raffsalvetti/FingerGrinder/pictures/2020-06-28 16.21.05_mod.jpg

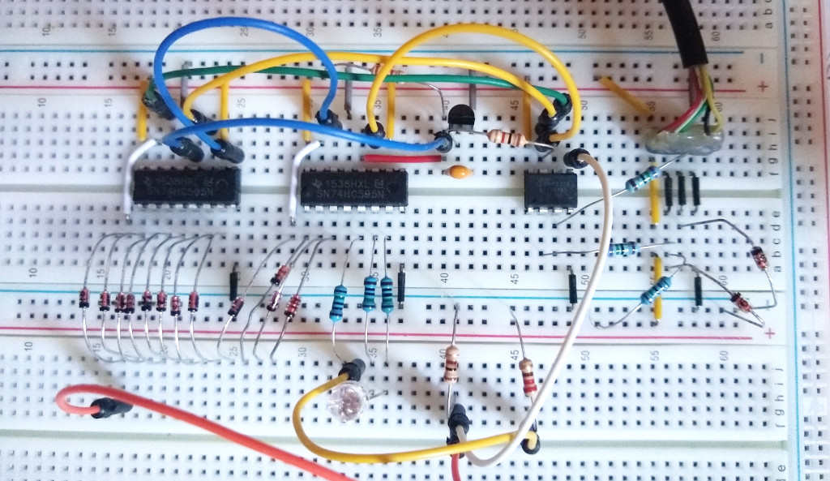
pictures/2020-06-28 16.21.05_mod.jpg
