raffsalvetti/FingerGrinder/pictures/2020-06-28 16.21.20.jpg

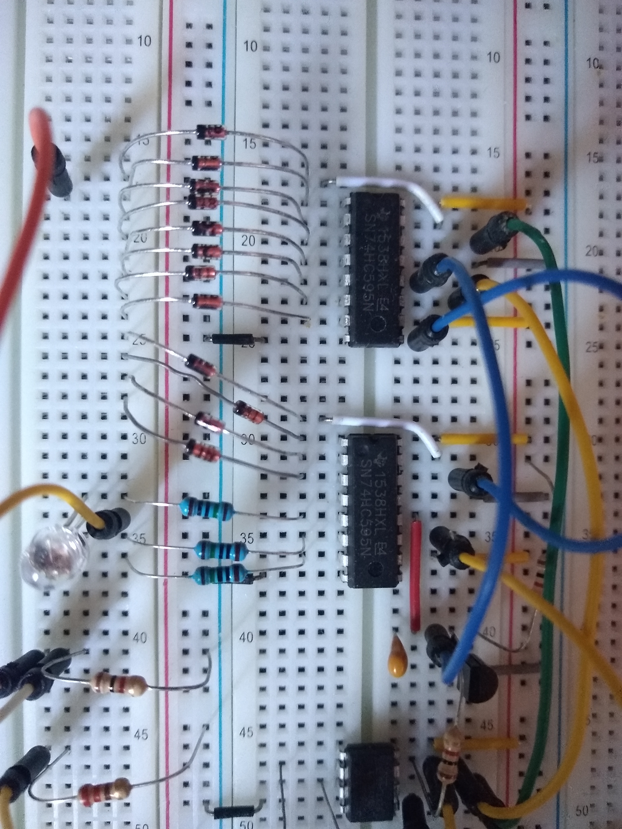
pictures/2020-06-28 16.21.20.jpg
