raffsalvetti/FingerGrinder/pictures/2020-07-19 19.21.56.jpg

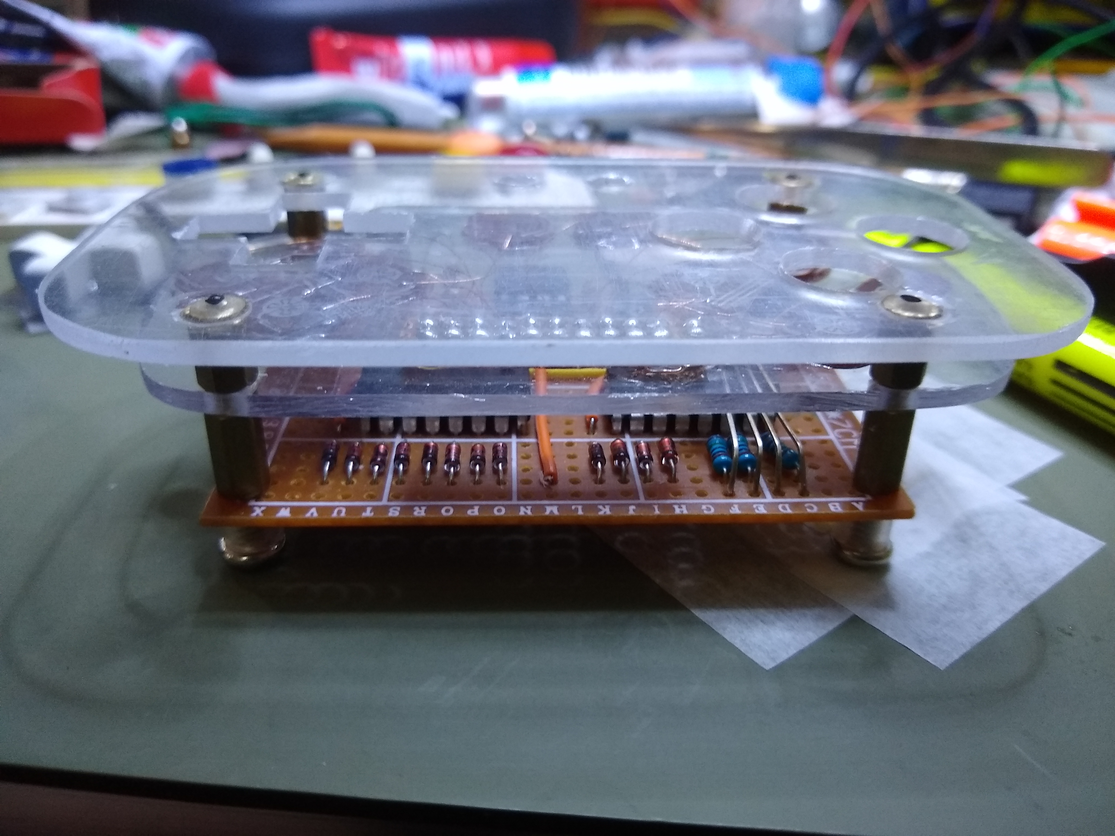
pictures/2020-07-19 19.21.56.jpg
