raffsalvetti/FingerGrinder/pictures/2020-07-19 19.22.34.jpg

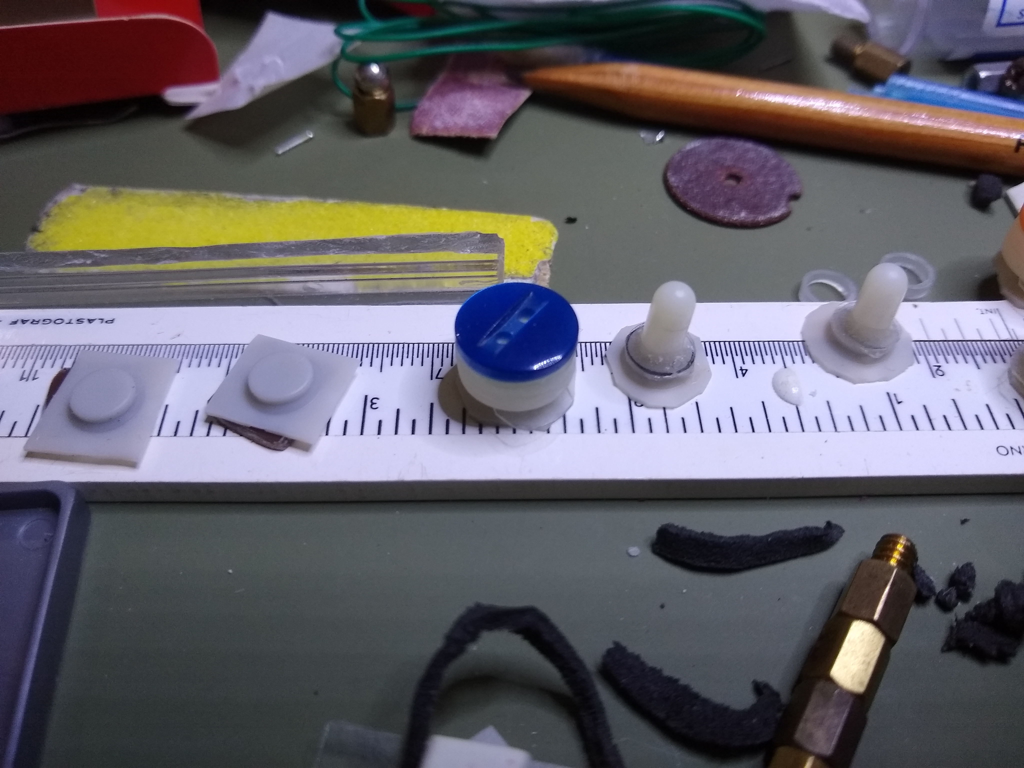
pictures/2020-07-19 19.22.34.jpg
