raffsalvetti/FingerGrinder/pictures/2020-07-19 19.22.51_mod.jpg

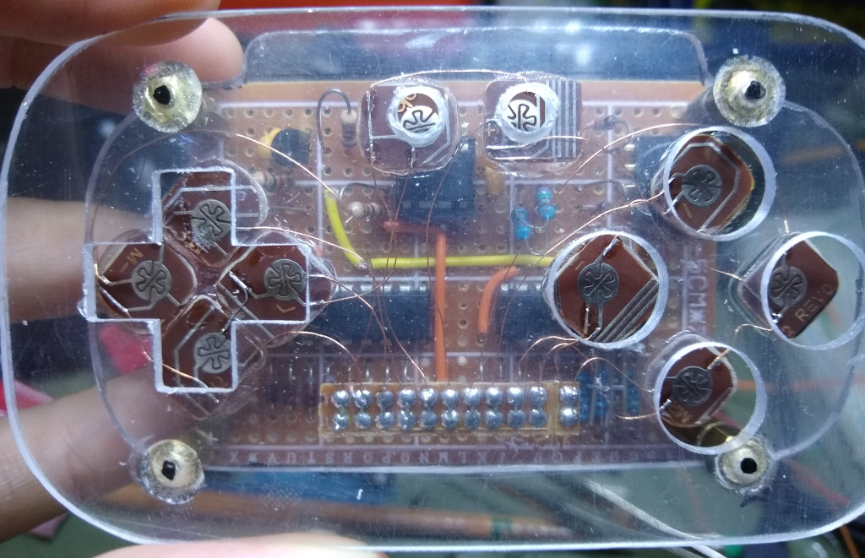
pictures/2020-07-19 19.22.51_mod.jpg
