raffsalvetti/FingerGrinder/pictures/2020-07-19 19.23.18.jpg

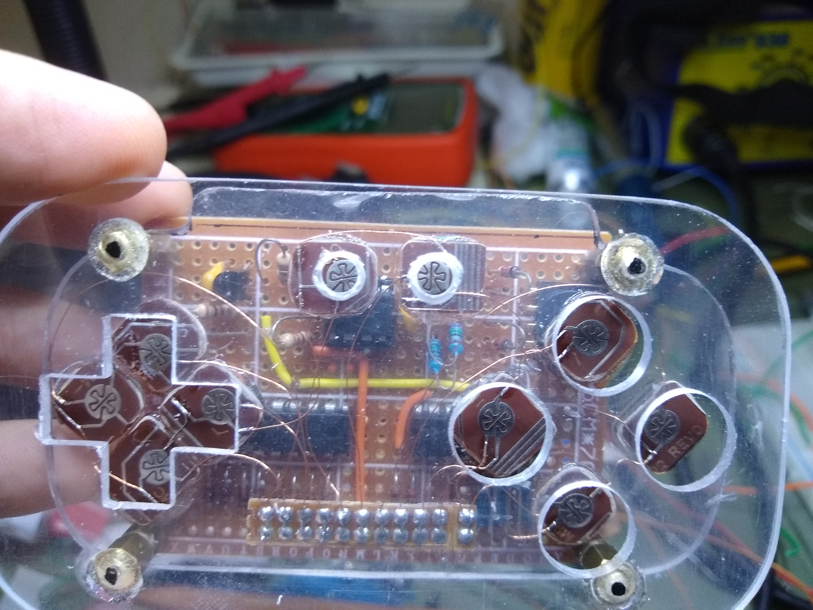
pictures/2020-07-19 19.23.18.jpg
