raffsalvetti/FingerGrinder/pictures/2020-07-19 19.24.29.jpg

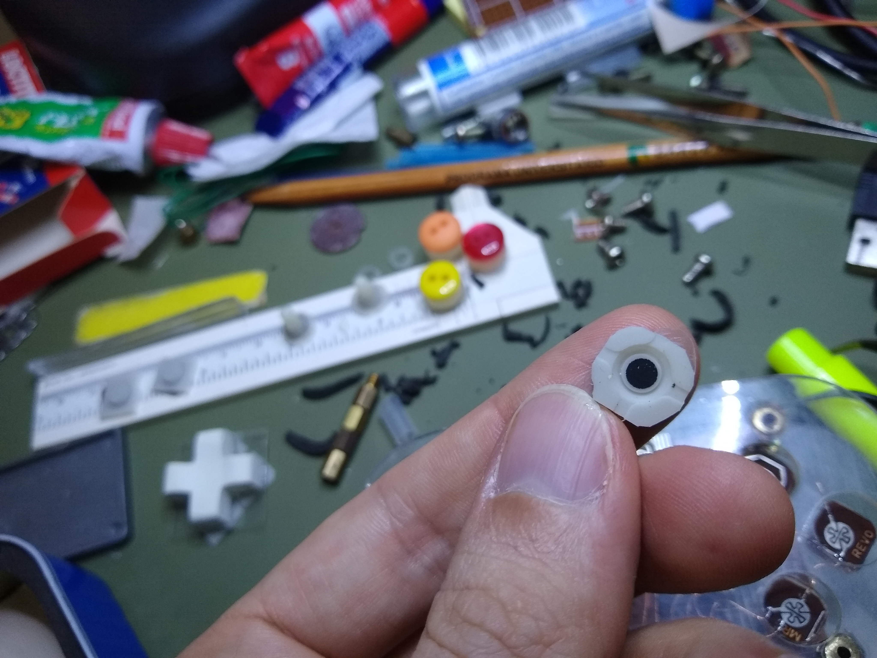
pictures/2020-07-19 19.24.29.jpg
