raffsalvetti/FingerGrinder/pictures/2020-07-21 17.19.35.jpg

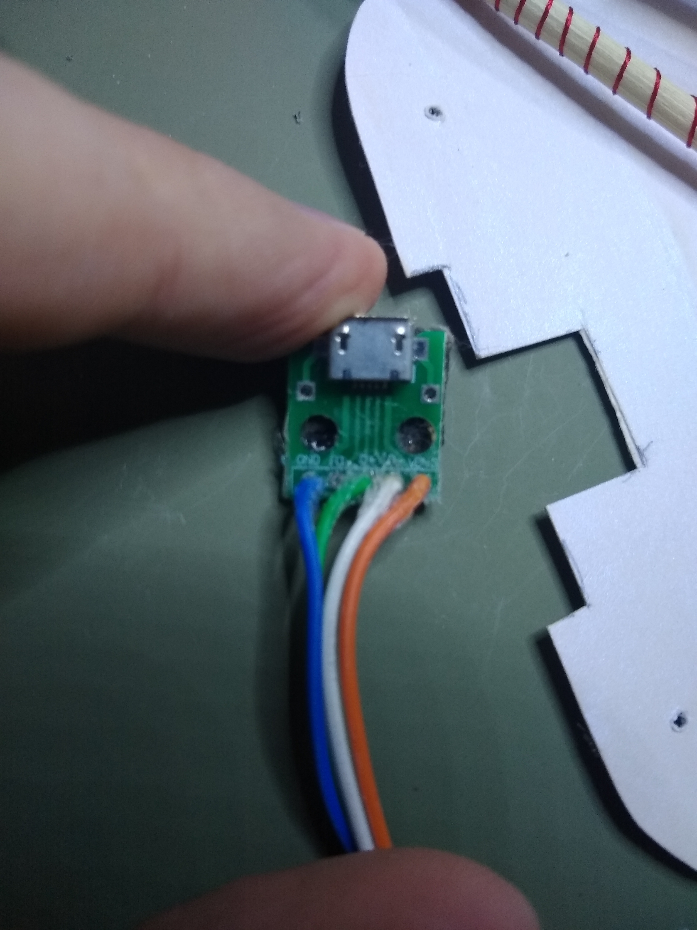
pictures/2020-07-21 17.19.35.jpg
