raffsalvetti/FingerGrinder/pictures/2020-07-24 15.05.28.jpg

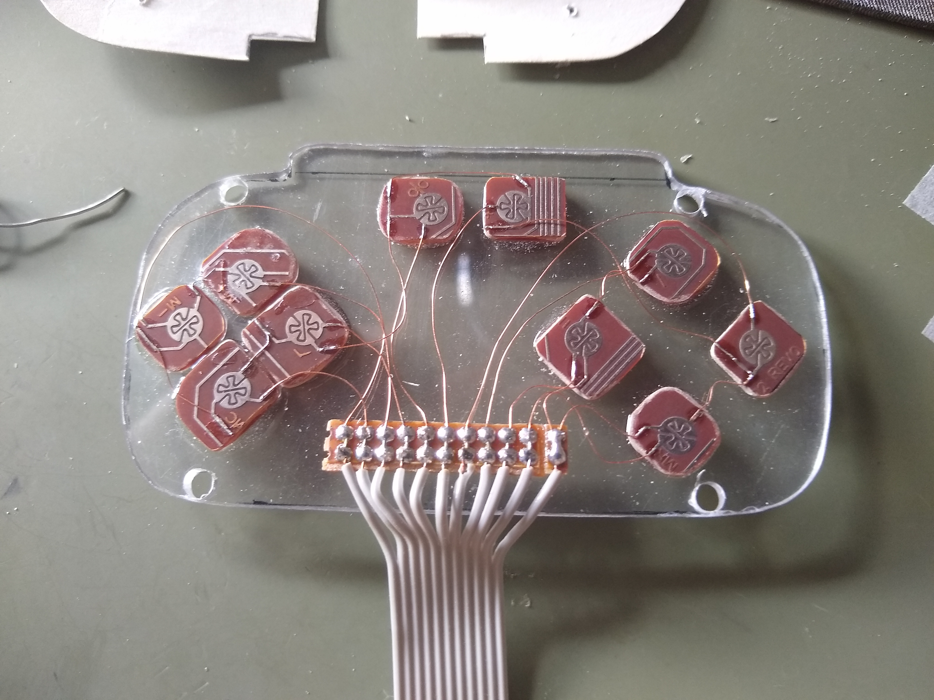
pictures/2020-07-24 15.05.28.jpg
