raffsalvetti/FingerGrinder/pictures/2020-07-24 19.13.18.jpg

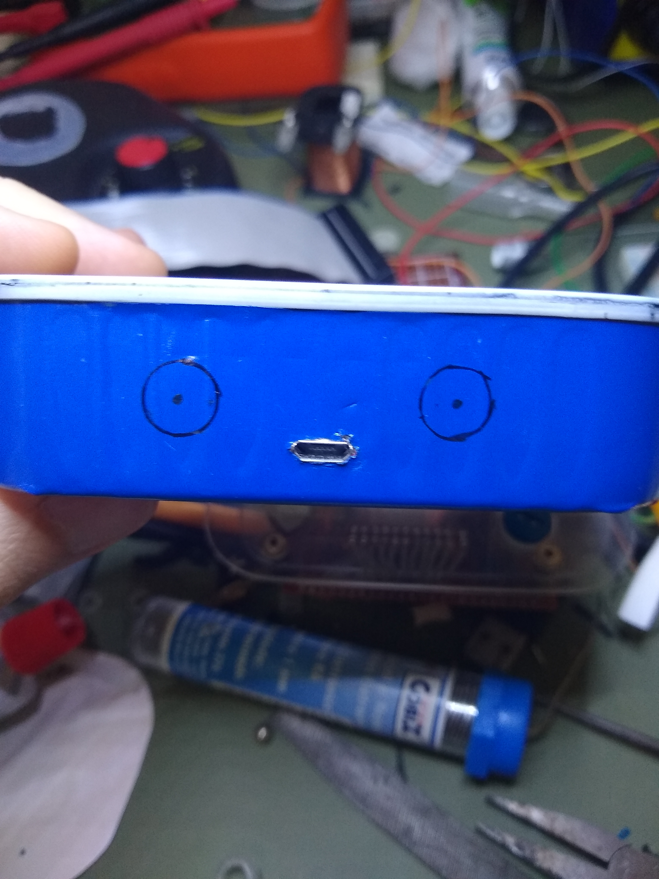
pictures/2020-07-24 19.13.18.jpg
