raffsalvetti/FingerGrinder/pictures/2020-07-25 12.25.55.jpg

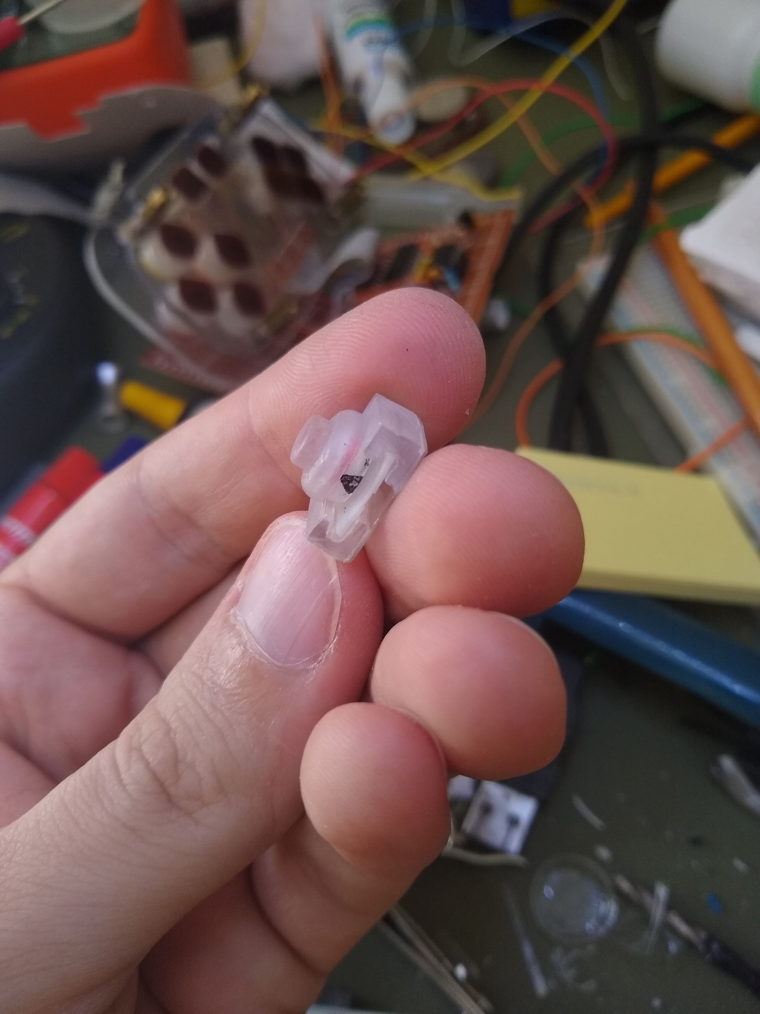
pictures/2020-07-25 12.25.55.jpg
