raffsalvetti/FingerGrinder/pictures/2020-07-25 12.26.28.jpg

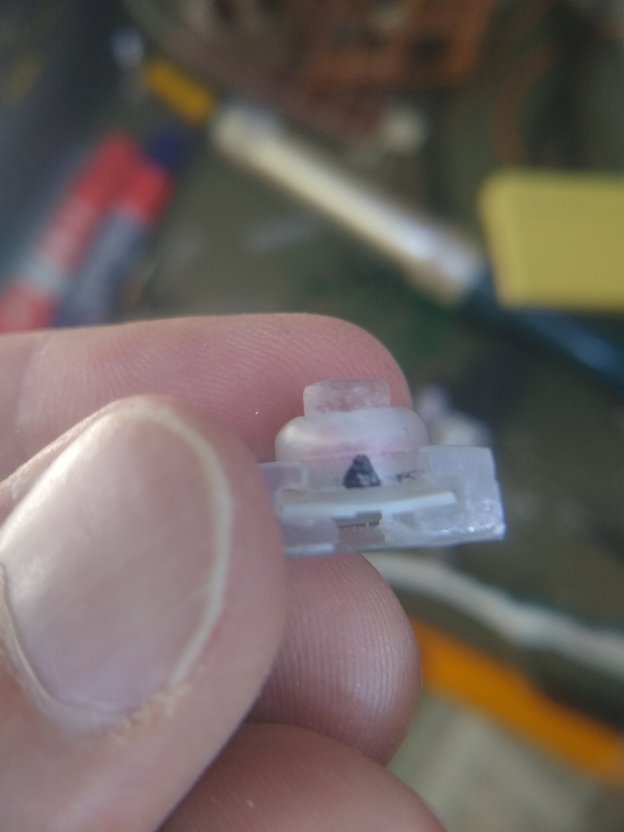
pictures/2020-07-25 12.26.28.jpg
