raffsalvetti/FingerGrinder/pictures/2020-07-25 12.27.35.jpg

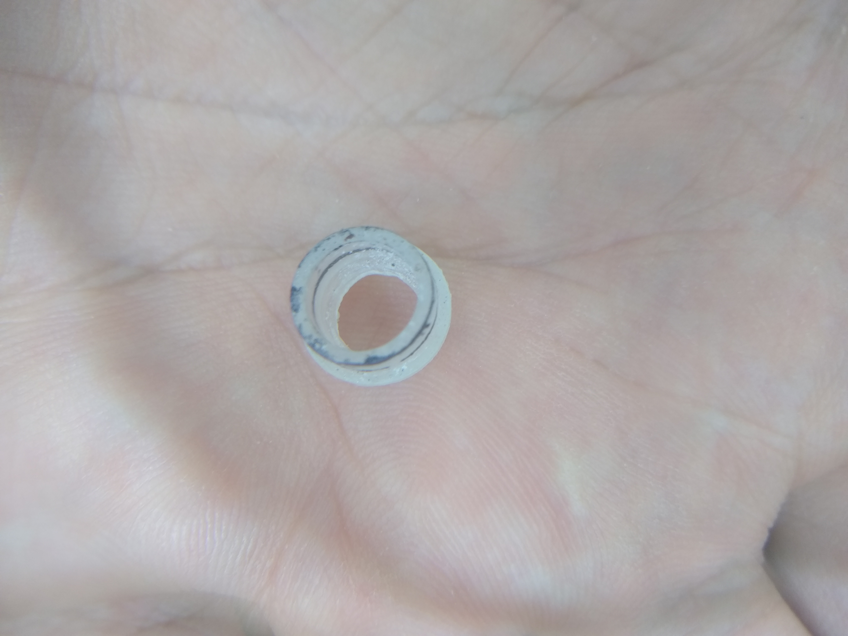
pictures/2020-07-25 12.27.35.jpg
