raffsalvetti/FingerGrinder/pictures/2020-07-25 12.28.15.jpg

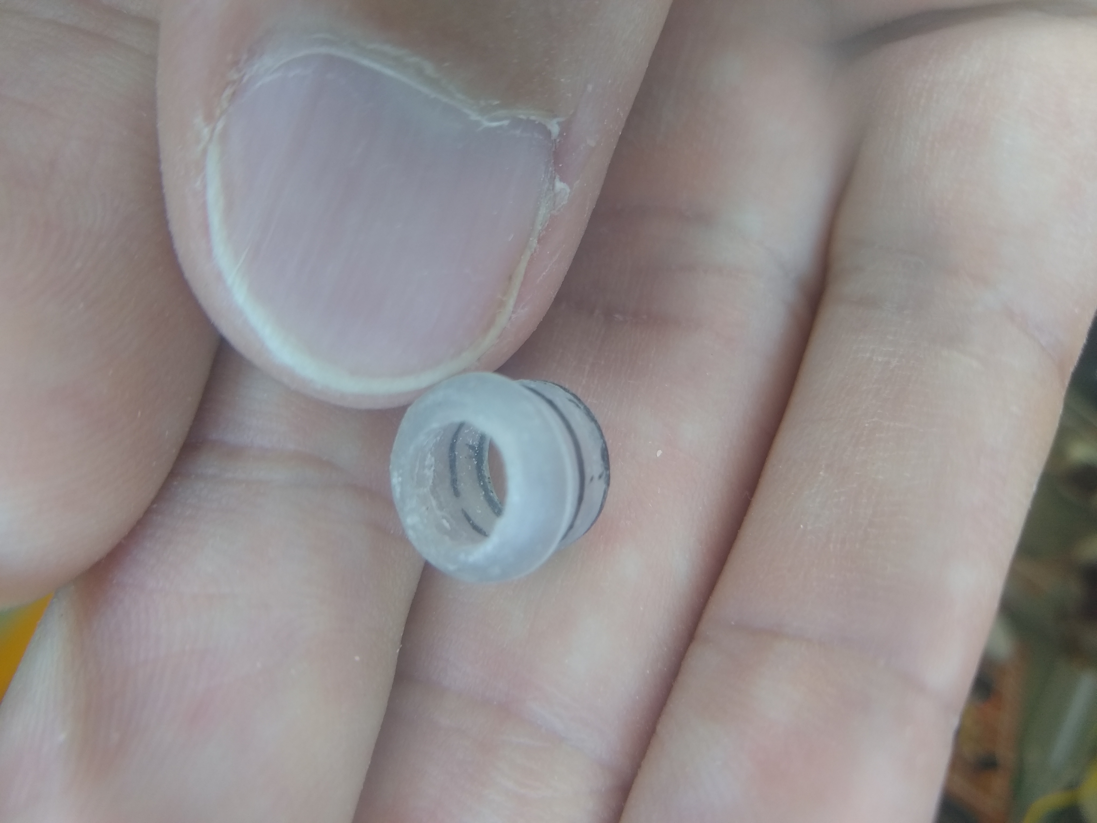
pictures/2020-07-25 12.28.15.jpg
