raffsalvetti/FingerGrinder/pictures/2020-07-25 12.28.40.jpg

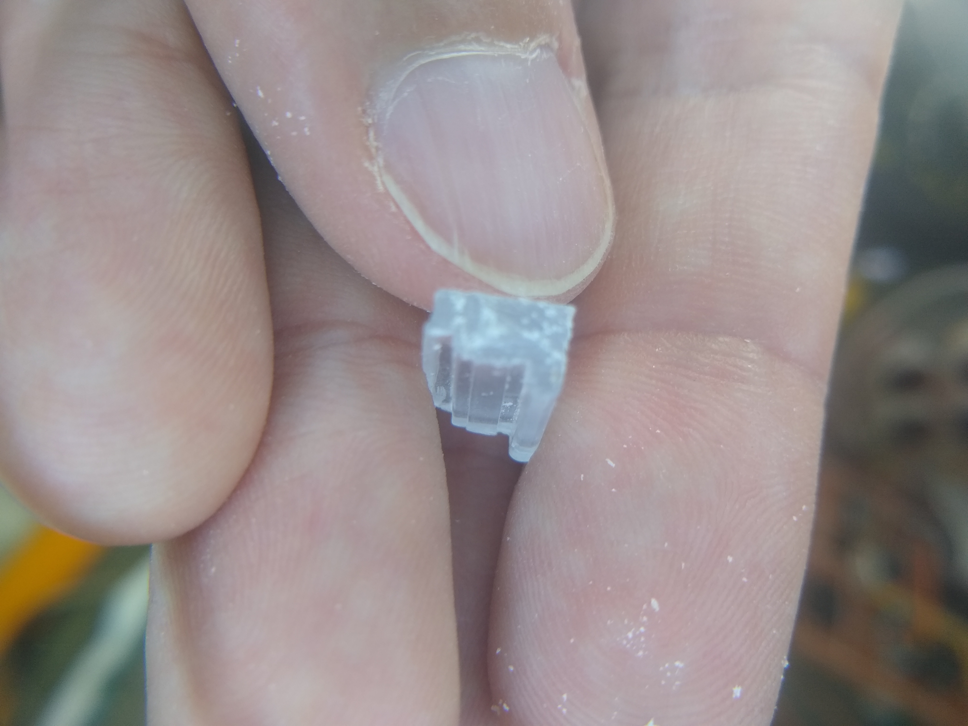
pictures/2020-07-25 12.28.40.jpg
