raffsalvetti/FingerGrinder/pictures/2020-07-25 12.29.03.jpg

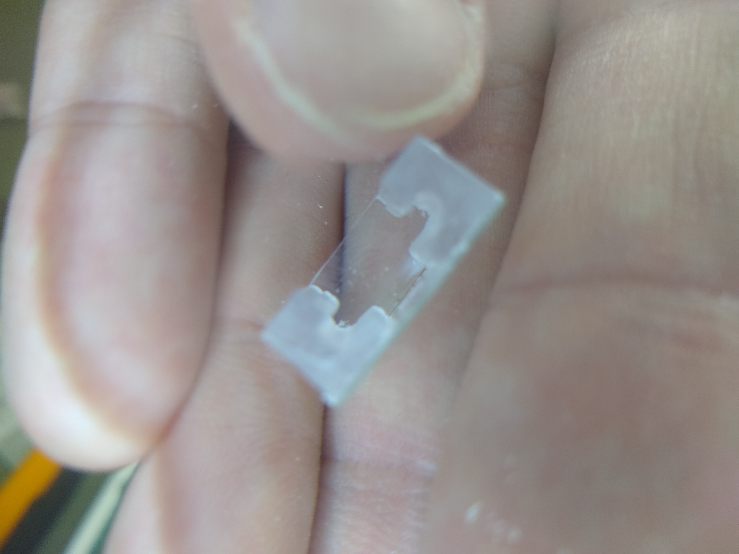
pictures/2020-07-25 12.29.03.jpg
