raffsalvetti/FingerGrinder/pictures/2020-07-25 12.29.58.jpg

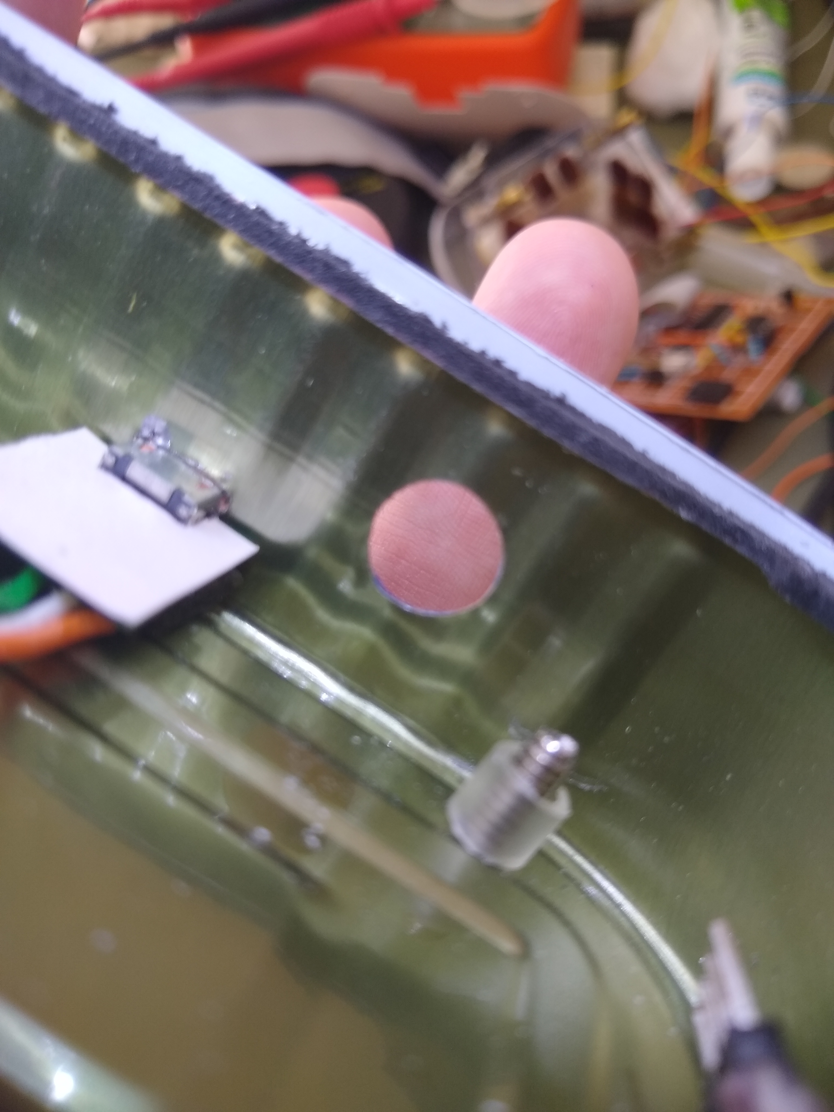
pictures/2020-07-25 12.29.58.jpg
