raffsalvetti/FingerGrinder/pictures/2020-07-26 18.45.50.jpg

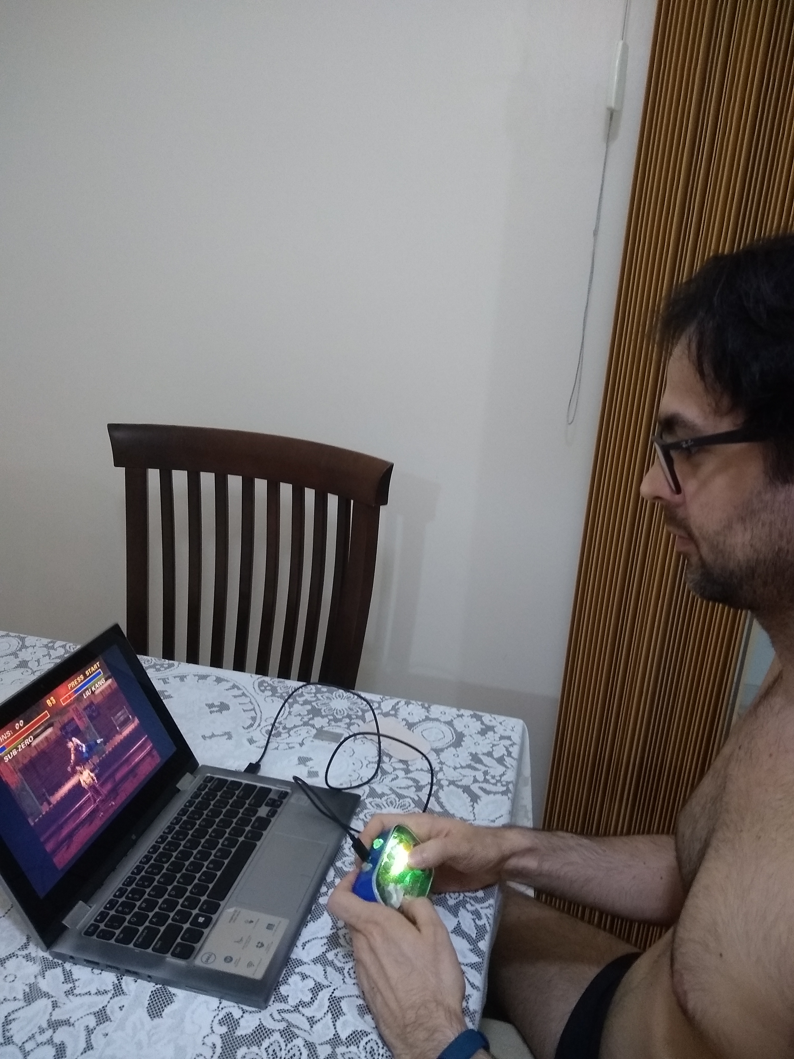
pictures/2020-07-26 18.45.50.jpg
