raffsalvetti/FingerGrinder/pictures/2020-07-29 21.15.36.jpg

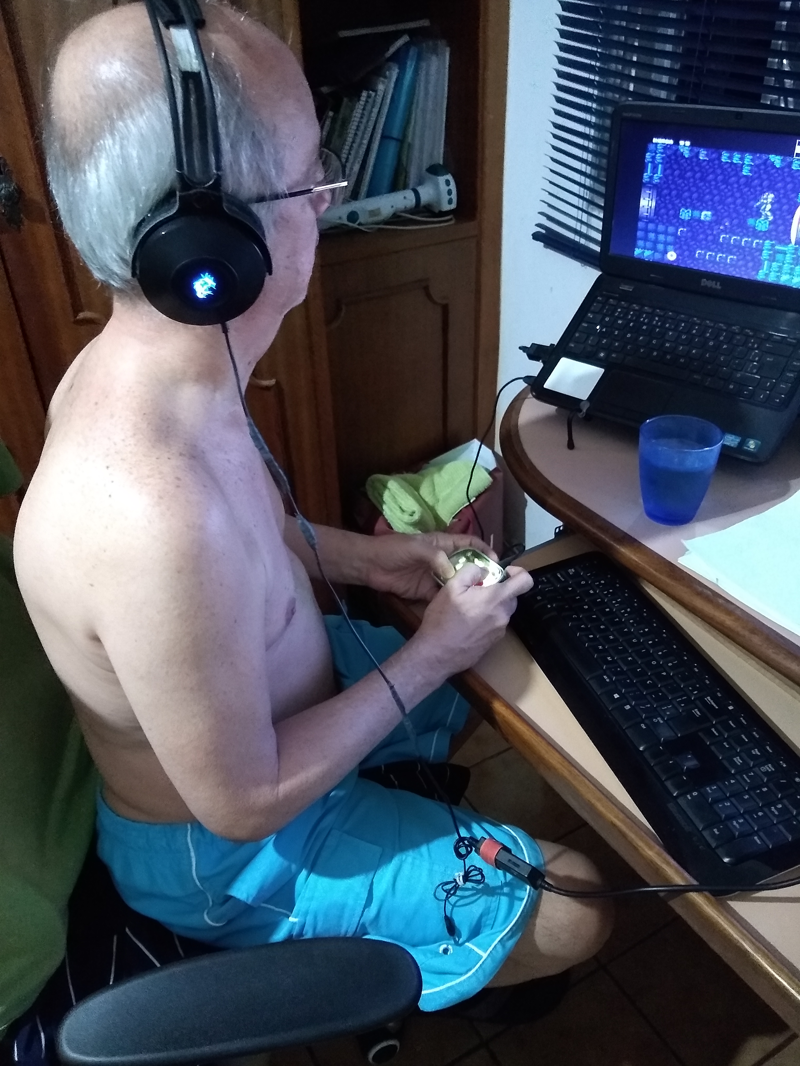
pictures/2020-07-29 21.15.36.jpg
