raffsalvetti/FingerGrinder/pictures/2020-07-29 21.16.27.jpg

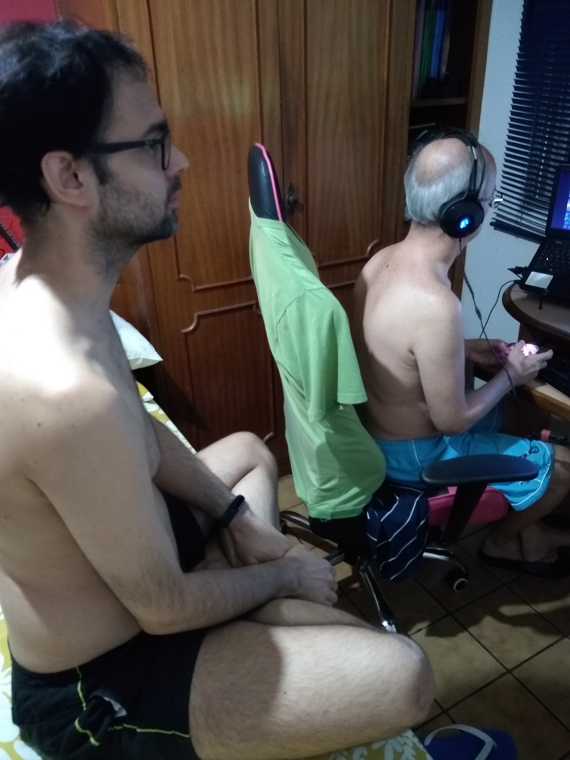
pictures/2020-07-29 21.16.27.jpg
