raffsalvetti/FingerGrinder/pictures/composition.jpg

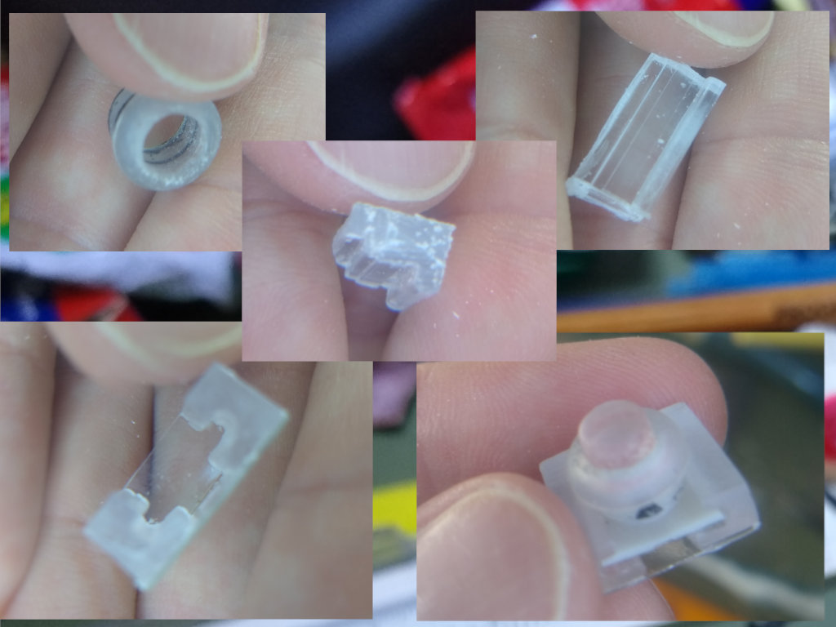
pictures/composition.jpg
