raffsalvetti/FingerGrinder/pictures/output.gif

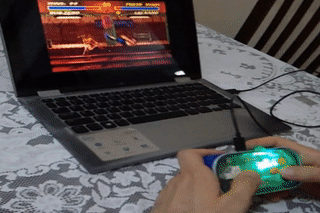
pictures/output.gif
